LuckyDogzyc/esp32-epaper-badge/esp32-epaper.kicad_sch

## KiCad design esp32-epaper.kicad_sch (2026-08-21)

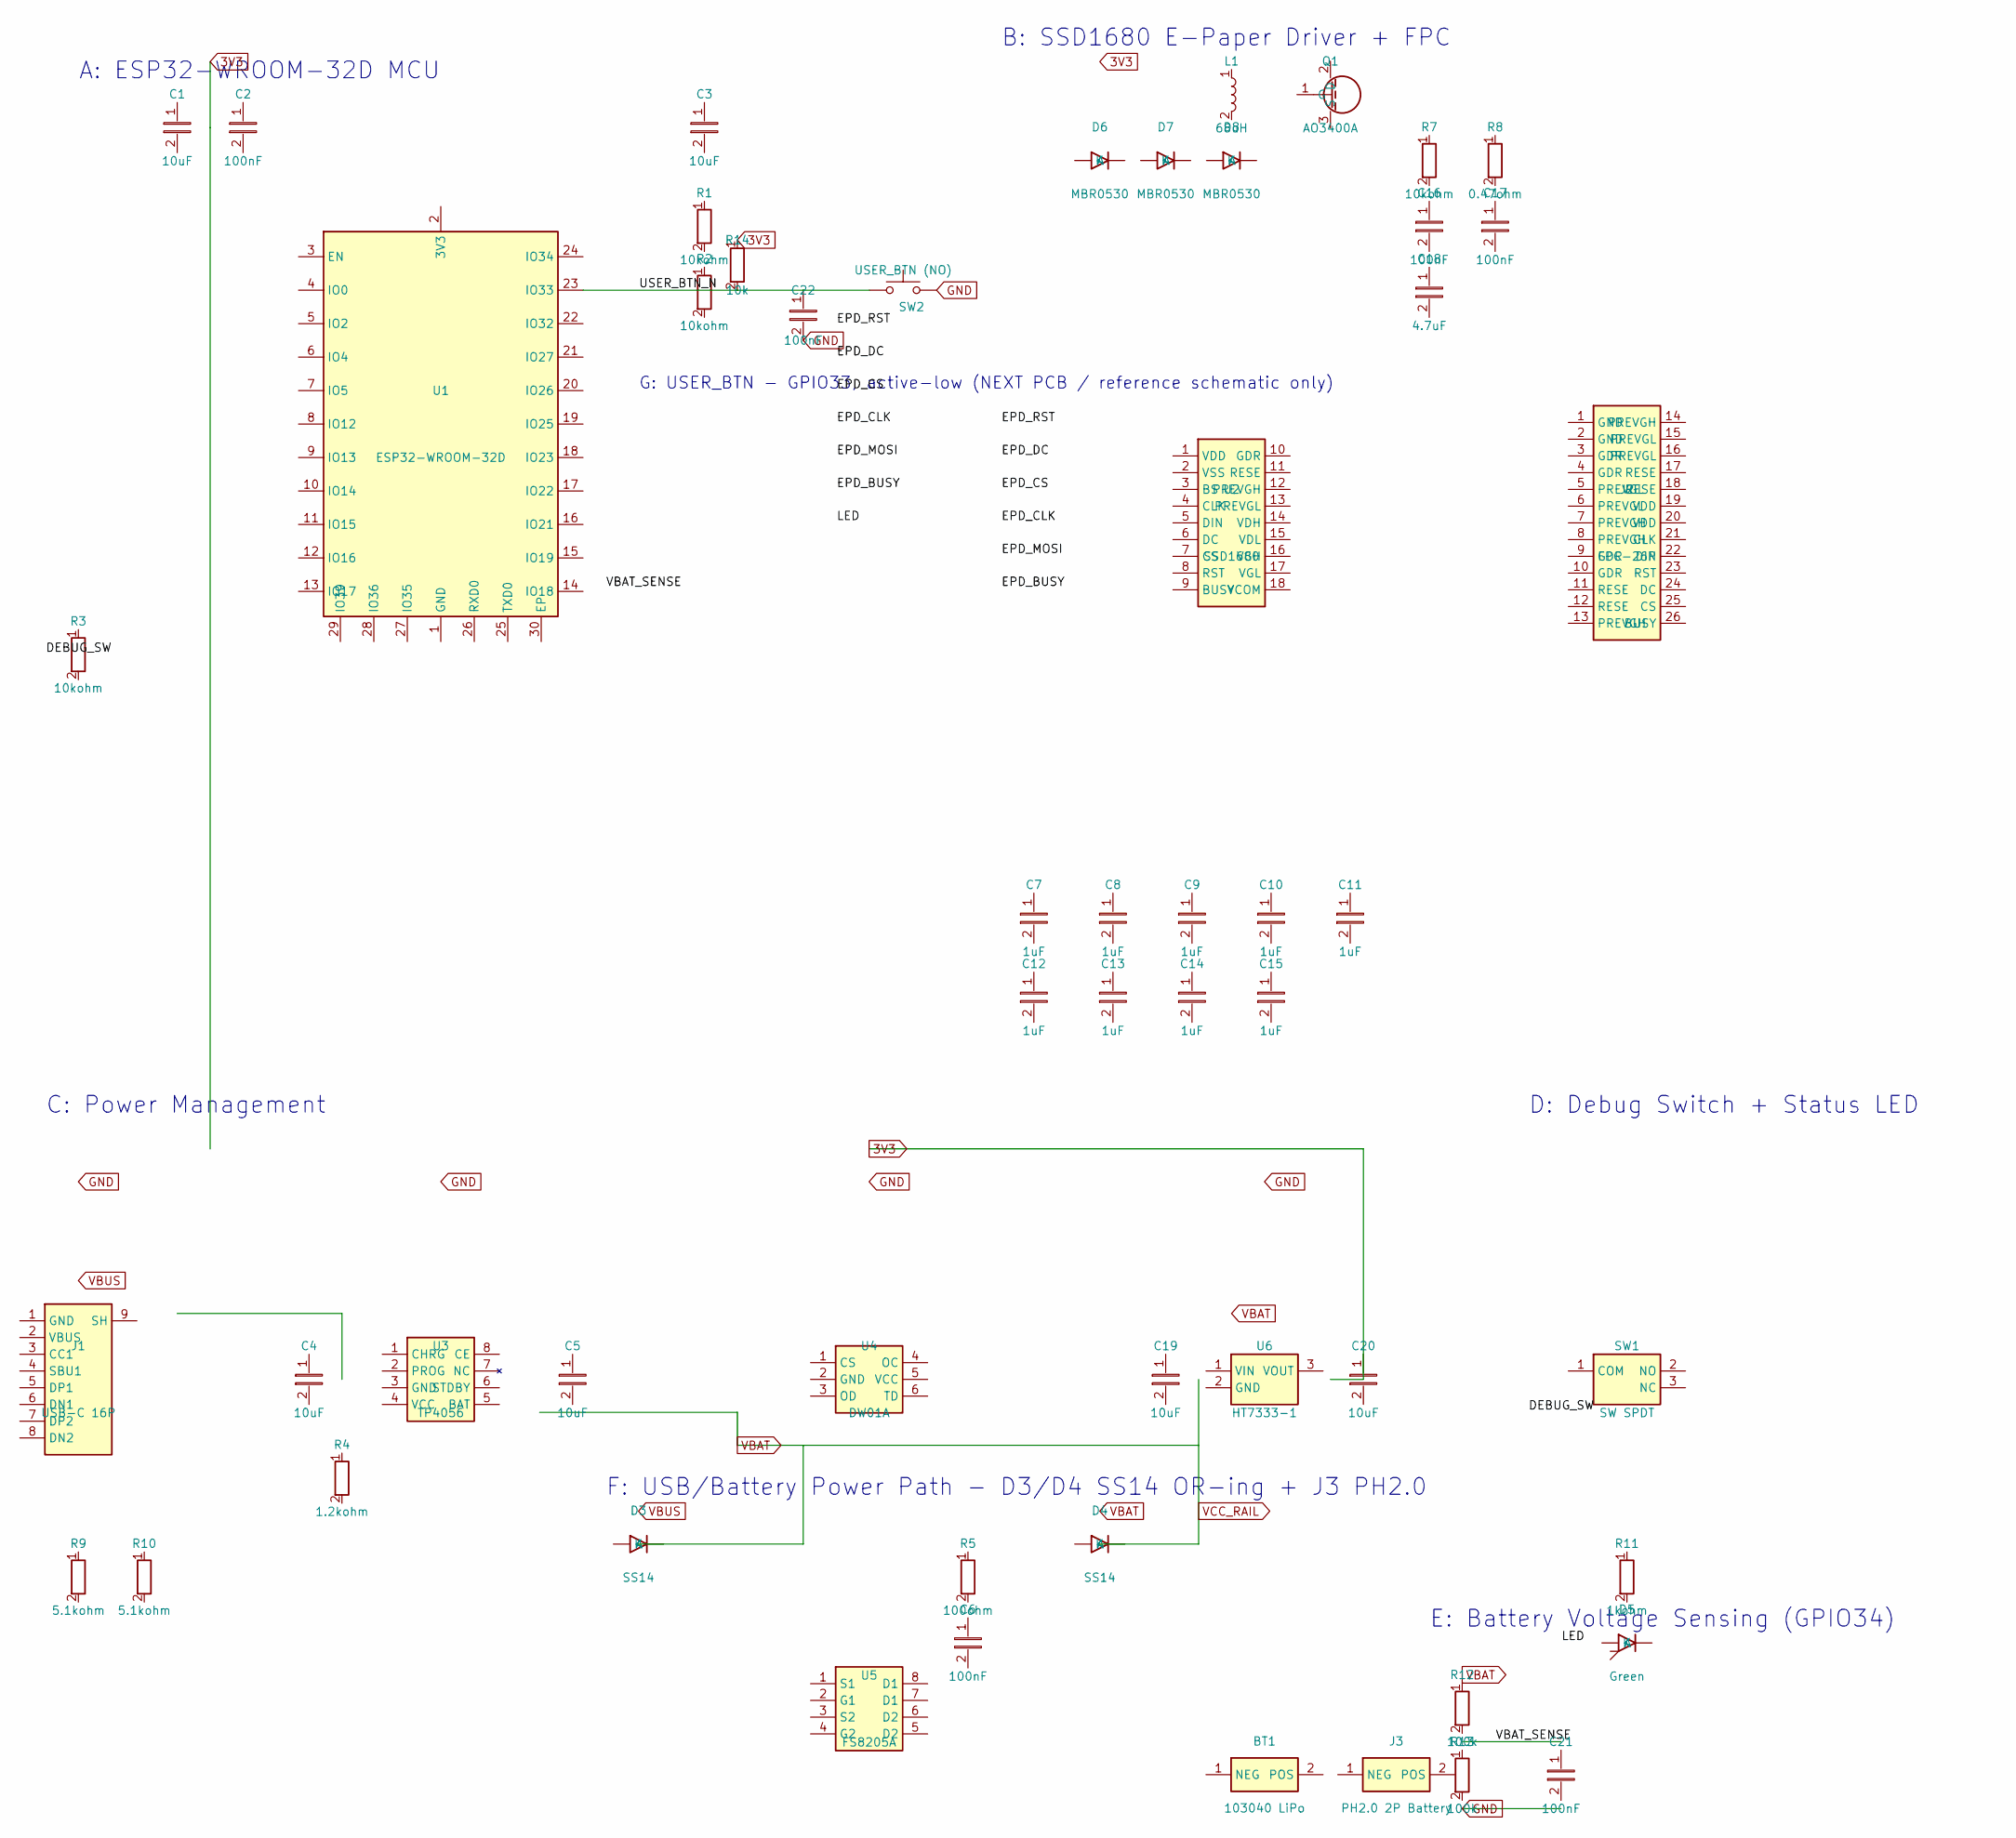
[picture p2: schematic esp32-epaper.kicad_sch]

Parts:
BT1: 103040 LiPo
C1, C3, C4, C5, C19, C20: 10uF
C2, C6, C16, C17, C21: 100nF
C7, C8, C9, C10, C11, C12, C13, C14, C15: 1uF
C18: 4.7uF
C22: 100nF; C_0603_1608Metric
D3, D4: SS14; D_SMA
D5: Green
D6, D7, D8: MBR0530
J1: USB-C 16P
J2: FPC-26P
J3: PH2.0 2P Battery; JST_PH_B2B-PH-K_1x02_P2.00mm_Vertical
L1: 68uH
Q1: AO3400A
R1, R2, R3, R7: 10kohm
R4: 1.2kohm
R5: 100ohm
R8: 0.47ohm
R9, R10: 5.1kohm
R11: 1kohm
R12, R13: 100k
R14: 10k; R_0603_1608Metric
SW1: SW SPDT
SW2: USER_BTN (NO); SW_SPST_TL3301AN
U1: ESP32-WROOM-32D
U2: SSD1680
U3: TP4056
U4: DW01A
U5: FS8205A
U6: HT7333-1

Connections:
3V3: R14.1
GND: C22.2, SW2.2
USER_BTN_N: C22.1, R14.2, SW2.1, U1.23 (IO33)

Notes on the sheet:
G: USER_BTN - GPIO33, active-low (NEXT PCB / reference schematic only)
F: USB/Battery Power Path - D3/D4 SS14 OR-ing + J3 PH2.0
E: Battery Voltage Sensing (GPIO34)
A: ESP32-WROOM-32D MCU
B: SSD1680 E-Paper Driver + FPC
C: Power Management
D: Debug Switch + Status LED
