LuckyDogzyc/esp32-epaper-badge/fix_lib_symbols.py

#!/usr/bin/env python3
"""Insert 7 missing standard KiCad library symbols into the schematic."""
import os

OUT = os.path.dirname(os.path.abspath(__file__))

# Standard KiCad device symbols that were missing
DEVICE_C = '''    (symbol "Device:C" (pin_names (offset 1.016) hide) (in_bom yes) (on_board yes)
      (property "Reference" "C" (at 0.635 2.54 0)
        (effects (font (size 1.27 1.27)) (justify left))
      )
      (property "Value" "C" (at 0.635 -2.54 0)
        (effects (font (size 1.27 1.27)) (justify left))
      )
      (property "Footprint" "" (at 0.9652 -3.81 0)
        (effects (font (size 1.27 1.27)) hide)
      )
      (rectangle (start -2.032 -0.762) (end 2.032 -0.508)
        (stroke (width 0)) (fill (type none))
      )
      (rectangle (start -2.032 0.508) (end 2.032 0.762)
        (stroke (width 0)) (fill (type none))
      )
      (pin passive line (at 0 3.81 270) (length 2.794)
        (name "~" (effects (font (size 1.27 1.27))))
        (number "1" (effects (font (size 1.27 1.27))))
      )
      (pin passive line (at 0 -3.81 90) (length 2.794)
        (name "~" (effects (font (size 1.27 1.27))))
        (number "2" (effects (font (size 1.27 1.27))))
      )
    )'''

DEVICE_R = '''    (symbol "Device:R" (in_bom yes) (on_board yes)
      (property "Reference" "R" (at 2.032 0 90)
        (effects (font (size 1.27 1.27)))
      )
      (property "Value" "R" (at 0 0 90)
        (effects (font (size 1.27 1.27)))
      )
      (property "Footprint" "" (at -3.81 0 90)
        (effects (font (size 1.27 1.27)) hide)
      )
      (rectangle (start -1.016 -2.54) (end 1.016 2.54)
        (stroke (width 0.254)) (fill (type none))
      )
      (pin passive line (at 0 3.81 270) (length 1.27)
        (name "~" (effects (font (size 1.27 1.27))))
        (number "1" (effects (font (size 1.27 1.27))))
      )
      (pin passive line (at 0 -3.81 90) (length 1.27)
        (name "~" (effects (font (size 1.27 1.27))))
        (number "2" (effects (font (size 1.27 1.27))))
      )
    )'''

DEVICE_D = '''    (symbol "Device:D" (pin_numbers hide) (in_bom yes) (on_board yes)
      (property "Reference" "D" (at 0 2.54 0)
        (effects (font (size 1.27 1.27)))
      )
      (property "Value" "D" (at 0 -2.54 0)
        (effects (font (size 1.27 1.27)))
      )
      (property "Footprint" "" (at 0 0 0)
        (effects (font (size 1.27 1.27)) hide)
      )
      (polyline (pts (xy -1.27 1.27) (xy -1.27 -1.27) (xy 1.27 0) (xy -1.27 1.27))
        (stroke (width 0.254)) (fill (type none))
      )
      (polyline (pts (xy 1.27 1.27) (xy 1.27 -1.27))
        (stroke (width 0.254)) (fill (type none))
      )
      (pin passive line (at -3.81 0 0) (length 2.54)
        (name "K" (effects (font (size 1.27 1.27))))
        (number "1" (effects (font (size 1.27 1.27))))
      )
      (pin passive line (at 3.81 0 180) (length 2.54)
        (name "A" (effects (font (size 1.27 1.27))))
        (number "2" (effects (font (size 1.27 1.27))))
      )
    )'''

DEVICE_L = '''    (symbol "Device:L" (in_bom yes) (on_board yes)
      (property "Reference" "L" (at -1.016 0 90)
        (effects (font (size 1.27 1.27)))
      )
      (property "Value" "L" (at 1.524 0 90)
        (effects (font (size 1.27 1.27)))
      )
      (property "Footprint" "" (at 0 0 0)
        (effects (font (size 1.27 1.27)) hide)
      )
      (arc (start 0 -2.54) (mid 0.635 -1.905) (end 0 -1.27)
        (stroke (width 0)) (fill (type none))
      )
      (arc (start 0 -1.27) (mid 0.635 -0.635) (end 0 0)
        (stroke (width 0)) (fill (type none))
      )
      (arc (start 0 0) (mid 0.635 0.635) (end 0 1.27)
        (stroke (width 0)) (fill (type none))
      )
      (arc (start 0 1.27) (mid 0.635 1.905) (end 0 2.54)
        (stroke (width 0)) (fill (type none))
      )
      (pin passive line (at 0 3.81 270) (length 1.27)
        (name "~" (effects (font (size 1.27 1.27))))
        (number "1" (effects (font (size 1.27 1.27))))
      )
      (pin passive line (at 0 -3.81 90) (length 1.27)
        (name "~" (effects (font (size 1.27 1.27))))
        (number "2" (effects (font (size 1.27 1.27))))
      )
    )'''

DEVICE_LED = '''    (symbol "Device:LED" (pin_numbers hide) (in_bom yes) (on_board yes)
      (property "Reference" "D" (at 0 2.54 0)
        (effects (font (size 1.27 1.27)))
      )
      (property "Value" "LED" (at 0 -2.54 0)
        (effects (font (size 1.27 1.27)))
      )
      (property "Footprint" "" (at 0 0 0)
        (effects (font (size 1.27 1.27)) hide)
      )
      (polyline (pts (xy -1.27 1.27) (xy -1.27 -1.27) (xy 1.27 0) (xy -1.27 1.27))
        (stroke (width 0.254)) (fill (type none))
      )
      (polyline (pts (xy 1.27 1.27) (xy 1.27 -1.27))
        (stroke (width 0.254)) (fill (type none))
      )
      (polyline (pts (xy -1.27 -1.27) (xy -2.54 -2.54))
        (stroke (width 0)) (fill (type none))
      )
      (polyline (pts (xy -1.27 -1.27) (xy -2.54 -1.27))
        (stroke (width 0)) (fill (type none))
      )
      (pin passive line (at -3.81 0 0) (length 2.54)
        (name "K" (effects (font (size 1.27 1.27))))
        (number "1" (effects (font (size 1.27 1.27))))
      )
      (pin passive line (at 3.81 0 180) (length 2.54)
        (name "A" (effects (font (size 1.27 1.27))))
        (number "2" (effects (font (size 1.27 1.27))))
      )
    )'''

DEVICE_Q = '''    (symbol "Device:Q_NMOS_GSD" (in_bom yes) (on_board yes)
      (property "Reference" "Q" (at 5.08 1.27 0)
        (effects (font (size 1.27 1.27)) (justify left))
      )
      (property "Value" "Q_NMOS_GSD" (at 5.08 -1.27 0)
        (effects (font (size 1.27 1.27)) (justify left))
      )
      (property "Footprint" "" (at 0 0 0)
        (effects (font (size 1.27 1.27)) hide)
      )
      (polyline (pts (xy 0.254 0) (xy -2.54 0))
        (stroke (width 0)) (fill (type none))
      )
      (polyline (pts (xy 0.254 1.905) (xy 0.254 -1.905))
        (stroke (width 0.254)) (fill (type none))
      )
      (polyline (pts (xy 0.762 -1.27) (xy 0.762 -2.286))
        (stroke (width 0.254)) (fill (type none))
      )
      (polyline (pts (xy 0.762 0.508) (xy 0.762 -0.508))
        (stroke (width 0.254)) (fill (type none))
      )
      (polyline (pts (xy 0.762 2.286) (xy 0.762 1.27))
        (stroke (width 0.254)) (fill (type none))
      )
      (circle (center 1.778 0) (radius 2.794)
        (stroke (width 0.254)) (fill (type none))
      )
      (pin input line (at -5.08 0 0) (length 2.54)
        (name "G" (effects (font (size 1.27 1.27))))
        (number "1" (effects (font (size 1.27 1.27))))
      )
      (pin passive line (at 0 5.08 270) (length 2.54)
        (name "D" (effects (font (size 1.27 1.27))))
        (number "2" (effects (font (size 1.27 1.27))))
      )
      (pin passive line (at 0 -5.08 90) (length 2.54)
        (name "S" (effects (font (size 1.27 1.27))))
        (number "3" (effects (font (size 1.27 1.27))))
      )
    )'''

ESP32 = '''    (symbol "RF_Module:ESP32-WROOM-32D" (in_bom yes) (on_board yes)
      (property "Reference" "U" (at -17.78 30.48 0)
        (effects (font (size 1.27 1.27)) (justify left))
      )
      (property "Value" "ESP32-WROOM-32D" (at 2.54 30.48 0)
        (effects (font (size 1.27 1.27)) (justify left))
      )
      (property "Footprint" "RF_Module:ESP32-WROOM-32D" (at 0 -33.02 0)
        (effects (font (size 1.27 1.27)) hide)
      )
      (rectangle (start -17.78 29.21) (end 17.78 -29.21)
        (stroke (width 0.254)) (fill (type background))
      )
      (pin power_in line (at 0 -33.02 90) (length 3.81)
        (name "GND" (effects (font (size 1.27 1.27))))
        (number "1" (effects (font (size 1.27 1.27))))
      )
      (pin power_in line (at 0 33.02 270) (length 3.81)
        (name "3V3" (effects (font (size 1.27 1.27))))
        (number "2" (effects (font (size 1.27 1.27))))
      )
      (pin input line (at -21.59 25.4 0) (length 3.81)
        (name "EN" (effects (font (size 1.27 1.27))))
        (number "3" (effects (font (size 1.27 1.27))))
      )
      (pin bidirectional line (at -21.59 20.32 0) (length 3.81)
        (name "IO0" (effects (font (size 1.27 1.27))))
        (number "4" (effects (font (size 1.27 1.27))))
      )
      (pin bidirectional line (at -21.59 15.24 0) (length 3.81)
        (name "IO2" (effects (font (size 1.27 1.27))))
        (number "5" (effects (font (size 1.27 1.27))))
      )
      (pin bidirectional line (at -21.59 10.16 0) (length 3.81)
        (name "IO4" (effects (font (size 1.27 1.27))))
        (number "6" (effects (font (size 1.27 1.27))))
      )
      (pin bidirectional line (at -21.59 5.08 0) (length 3.81)
        (name "IO5" (effects (font (size 1.27 1.27))))
        (number "7" (effects (font (size 1.27 1.27))))
      )
      (pin bidirectional line (at -21.59 0 0) (length 3.81)
        (name "IO12" (effects (font (size 1.27 1.27))))
        (number "8" (effects (font (size 1.27 1.27))))
      )
      (pin bidirectional line (at -21.59 -5.08 0) (length 3.81)
        (name "IO13" (effects (font (size 1.27 1.27))))
        (number "9" (effects (font (size 1.27 1.27))))
      )
      (pin bidirectional line (at -21.59 -10.16 0) (length 3.81)
        (name "IO14" (effects (font (size 1.27 1.27))))
        (number "10" (effects (font (size 1.27 1.27))))
      )
      (pin bidirectional line (at -21.59 -15.24 0) (length 3.81)
        (name "IO15" (effects (font (size 1.27 1.27))))
        (number "11" (effects (font (size 1.27 1.27))))
      )
      (pin bidirectional line (at -21.59 -20.32 0) (length 3.81)
        (name "IO16" (effects (font (size 1.27 1.27))))
        (number "12" (effects (font (size 1.27 1.27))))
      )
      (pin bidirectional line (at -21.59 -25.4 0) (length 3.81)
        (name "IO17" (effects (font (size 1.27 1.27))))
        (number "13" (effects (font (size 1.27 1.27))))
      )
      (pin bidirectional line (at 21.59 -25.4 180) (length 3.81)
        (name "IO18" (effects (font (size 1.27 1.27))))
        (number "14" (effects (font (size 1.27 1.27))))
      )
      (pin bidirectional line (at 21.59 -20.32 180) (length 3.81)
        (name "IO19" (effects (font (size 1.27 1.27))))
        (number "15" (effects (font (size 1.27 1.27))))
      )
      (pin bidirectional line (at 21.59 -15.24 180) (length 3.81)
        (name "IO21" (effects (font (size 1.27 1.27))))
        (number "16" (effects (font (size 1.27 1.27))))
      )
      (pin bidirectional line (at 21.59 -10.16 180) (length 3.81)
        (name "IO22" (effects (font (size 1.27 1.27))))
        (number "17" (effects (font (size 1.27 1.27))))
      )
      (pin bidirectional line (at 21.59 -5.08 180) (length 3.81)
        (name "IO23" (effects (font (size 1.27 1.27))))
        (number "18" (effects (font (size 1.27 1.27))))
      )
      (pin input line (at 21.59 0 180) (length 3.81)
        (name "IO25" (effects (font (size 1.27 1.27))))
        (number "19" (effects (font (size 1.27 1.27))))
      )
      (pin input line (at 21.59 5.08 180) (length 3.81)
        (name "IO26" (effects (font (size 1.27 1.27))))
        (number "20" (effects (font (size 1.27 1.27))))
      )
      (pin input line (at 21.59 10.16 180) (length 3.81)
        (name "IO27" (effects (font (size 1.27 1.27))))
        (number "21" (effects (font (size 1.27 1.27))))
      )
      (pin bidirectional line (at 21.59 15.24 180) (length 3.81)
        (name "IO32" (effects (font (size 1.27 1.27))))
        (number "22" (effects (font (size 1.27 1.27))))
      )
      (pin bidirectional line (at 21.59 20.32 180) (length 3.81)
        (name "IO33" (effects (font (size 1.27 1.27))))
        (number "23" (effects (font (size 1.27 1.27))))
      )
      (pin bidirectional line (at 21.59 25.4 180) (length 3.81)
        (name "IO34" (effects (font (size 1.27 1.27))))
        (number "24" (effects (font (size 1.27 1.27))))
      )
      (pin output line (at 10.16 -33.02 90) (length 3.81)
        (name "TXD0" (effects (font (size 1.27 1.27))))
        (number "25" (effects (font (size 1.27 1.27))))
      )
      (pin input line (at 5.08 -33.02 90) (length 3.81)
        (name "RXD0" (effects (font (size 1.27 1.27))))
        (number "26" (effects (font (size 1.27 1.27))))
      )
      (pin output line (at -5.08 -33.02 90) (length 3.81)
        (name "IO35" (effects (font (size 1.27 1.27))))
        (number "27" (effects (font (size 1.27 1.27))))
      )
      (pin output line (at -10.16 -33.02 90) (length 3.81)
        (name "IO36" (effects (font (size 1.27 1.27))))
        (number "28" (effects (font (size 1.27 1.27))))
      )
      (pin output line (at -15.24 -33.02 90) (length 3.81)
        (name "IO39" (effects (font (size 1.27 1.27))))
        (number "29" (effects (font (size 1.27 1.27))))
      )
      (pin passive line (at 15.24 -33.02 90) (length 3.81)
        (name "EP" (effects (font (size 1.27 1.27))))
        (number "30" (effects (font (size 1.27 1.27))))
      )
    )'''

# Read the existing schematic
sch_path = os.path.join(OUT, 'esp32-epaper.kicad_sch')
with open(sch_path, 'r') as f:
    content = f.read()

# Find the lib_symbols closing bracket
# Look for "  )\n\n" after "(lib_symbols"
lib_idx = content.index('(lib_symbols')
close_idx = content.index('\n  )\n', lib_idx)

# Insert standard symbols before the closing bracket
insert = '\n'.join([DEVICE_C, DEVICE_R, DEVICE_D, DEVICE_L, DEVICE_LED, DEVICE_Q, ESP32])
content = content[:close_idx] + '\n' + insert + content[close_idx:]

# Fix ESP32 pin count: 39 -> 30 (matching our 30-pin lib symbol)
# Count pin UUIDs for ESP32 instance
esp32_idx = content.index('(lib_id "RF_Module:ESP32-WROOM-32D")')
esp32_end = content.index('\n  )\n', esp32_idx)

# Replace 39 pin UUIDs with 30
import re
esp32_block = content[esp32_idx:esp32_end]
pin_lines = re.findall(r'    \(pin "\d+" \(uuid [^)]+\)\)', esp32_block)
print(f"ESP32 has {len(pin_lines)} pin UUIDs (need 30)")

if len(pin_lines) > 30:
    # Remove extra pins (31-39)
    for p in pin_lines[30:]:
        esp32_block = esp32_block.replace(p, '', 1)
    content = content[:esp32_idx] + esp32_block + content[esp32_end:]
    print(f"Trimmed to 30 pins")

# Write back
with open(sch_path, 'w') as f:
    f.write(content)

# Verify: check all lib_ids now have matching definitions
lines = content.split('\n')
lib_ids = set()
inst_ids = set()
for line in lines:
    if '(symbol "' in line and 'lib_symbols' not in line:
        s = line.index('"') + 1
        e = line.index('"', s)
        lib_ids.add(line[s:e])
    if '(lib_id "' in line:
        s = line.index('"') + 1
        e = line.index('"', s)
        inst_ids.add(line[s:e])

missing = inst_ids - lib_ids
print(f"\nLib symbols: {len(lib_ids)}, Instances: {len(inst_ids)}")
if missing:
    print(f"STILL MISSING: {sorted(missing)}")
else:
    print("✓ All instance lib_ids have matching lib_symbols definitions!")

print(f"\nFile size: {len(content)} bytes")
